LeoLiu5/Air-Quality-Monitoring-Station-by-Leo-Liu/img/enclosure2.png

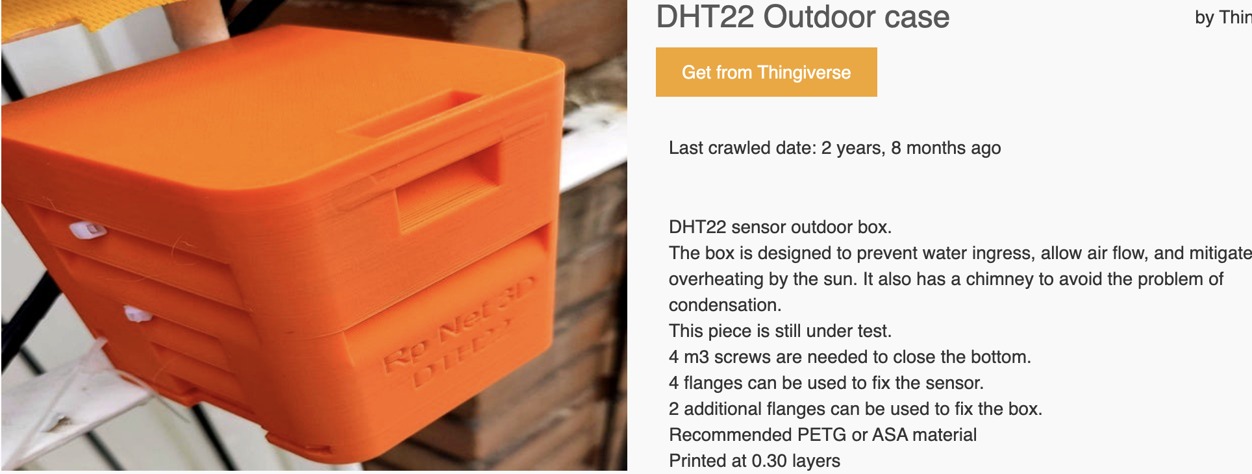
img/enclosure2.png
