LeoLiu5/Air-Quality-Monitoring-Station-by-Leo-Liu/img/enclosure.png

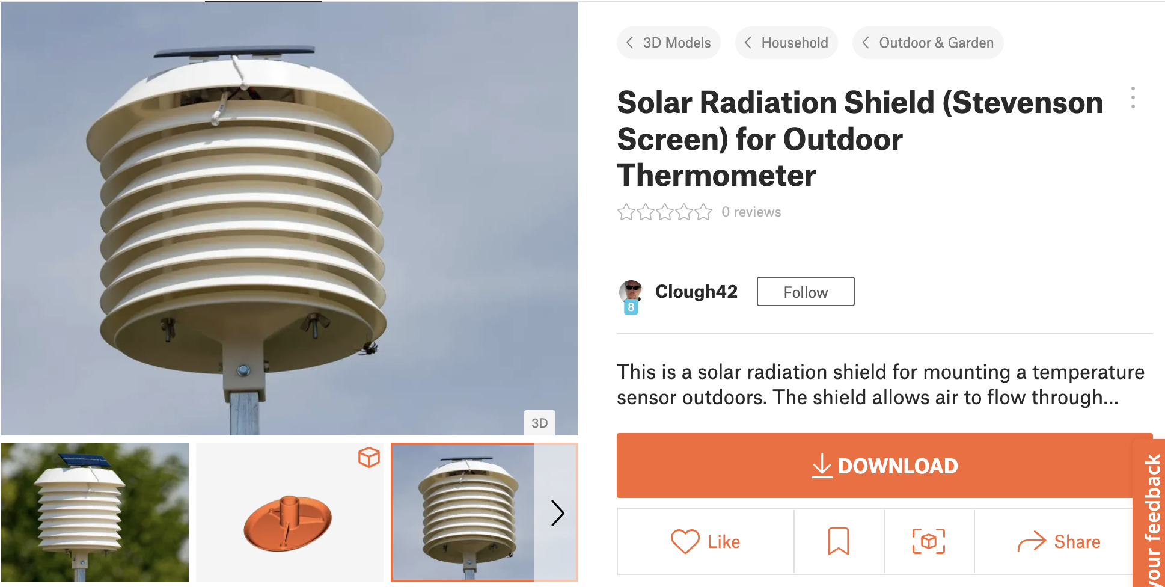
img/enclosure.png
