LeoLiu5/Air-Quality-Monitoring-Station-by-Leo-Liu/img/p0.jpeg

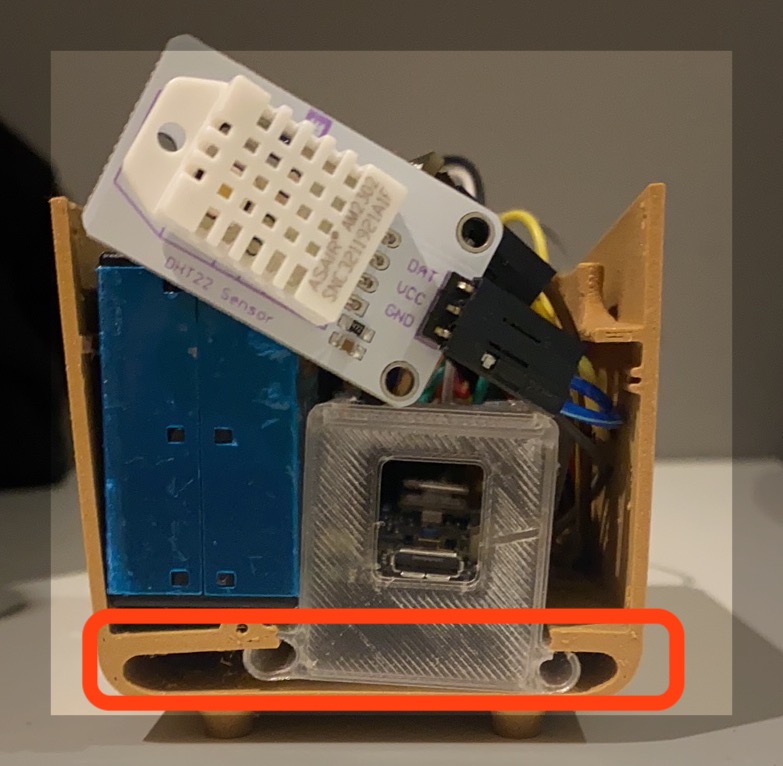
img/p0.jpeg
