LeoLiu5/Air-Quality-Monitoring-Station-by-Leo-Liu/img/p1.jpeg

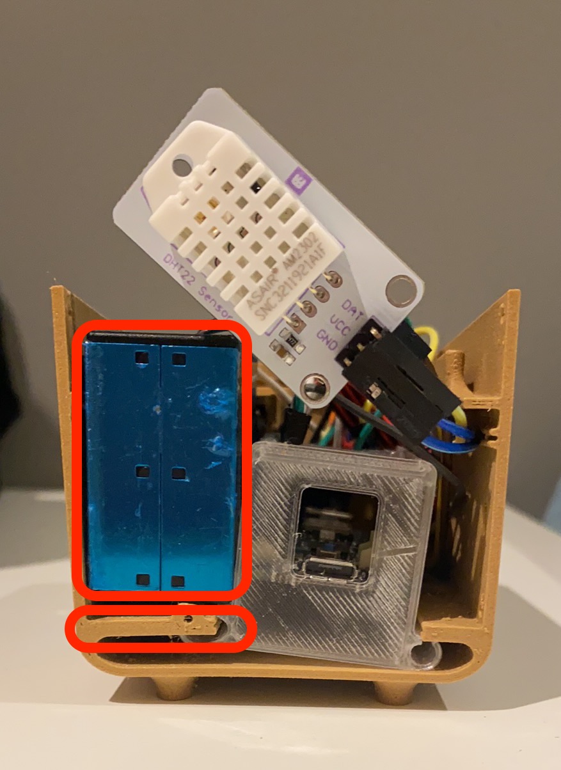
img/p1.jpeg
